gwilherm/midi-viscount-rte0616/firmware/firmware/USBMIDIInterface.h

#ifndef USB_MIDI_INTERFACE_H
#define USB_MIDI_INTERFACE_H

#include "IMIDIInterface.h"
#include "MIDIConfig.h"

#include <USB-MIDI.h>

class USBMIDIInterface : public IMIDIInterface {
public:
    USBMIDIInterface();
    virtual ~USBMIDIInterface() = default;

    void setup();
    void loop();

    virtual void sendSysEx(unsigned inLength,
                          const uint8_t* inArray);

    virtual void setHandleSystemExclusive(void (*fptr)(uint8_t * array, unsigned size));

    virtual void sendNote(IMIDIInterface::note_state_t state,
                          uint8_t inNoteNumber,
                          uint8_t inChannel);

    virtual void sendCC(uint8_t inControlNumber,
                        uint8_t inControlValue,
                        uint8_t inChannel);
protected:
    USBMIDI_NAMESPACE::usbMidiTransport _usbMidi;
    MIDI_NAMESPACE::MidiInterface<USBMIDI_NAMESPACE::usbMidiTransport> _usbMidiInterface;
};

#endif
