gwilherm/midi-viscount-rte0616/firmware/test/testsuite/MIDISysexServiceTest.cpp

#include <gtest/gtest.h>
#include <cstdint>

#include "SerialPrinter.h"
#include "MIDIConfig.h"
#include "CalibrationConfig.h"
#include "USBMIDIMock.h"
#include "MemoryServiceMock.h"
#include "MIDISysexService.h"

SerialPrinter Serial;

#define EXPECT_SYSEX(e) [&](unsigned size, const uint8_t* array) { \
    EXPECT_EQ(size, sizeof(e)); \
    for (int i = 0; i < sizeof(e); i++) \
        EXPECT_EQ(array[i], e[i]); \
}

class MIDISysexServiceTest : public ::testing::Test {
public:
    MIDISysexServiceTest() : _sysexService(_usbMidiMock, _midiConfig, _calibrationConfig, _memServiceMock)
    {};

    void SetUp(void) {
        _midiConfig.reset();
        _calibrationConfig.reset();
    }

protected:
    MidiConfig _midiConfig;
    CalibrationConfig _calibrationConfig;
    ::testing::StrictMock<USBMIDIMock> _usbMidiMock;
    MemoryServiceMock _memServiceMock;
    MIDISysexService _sysexService;
};

TEST_F(MIDISysexServiceTest, handle_ident_msg)
{
    // Ident request
    uint8_t req[] = { 0xF0, 0x7E, 0x7F, 0x06, 0x01, 0xF7 };
    //                                 chan,                     f1,   f2,   p1,   p2,   v1,   v2,   v3,   v4
    const uint8_t exp_resp[] = { 0x7E, 0x01, 0x06, 0x02, 0x31, 0x00, 0x31, 0x06, 0x16, 0x01, 0x02, 0x00, 0x03 };

    using namespace ::testing;
    EXPECT_CALL(_usbMidiMock, sendSysEx(_, _))
    .WillOnce(Invoke(EXPECT_SYSEX(exp_resp)));

    _sysexService.handleSysEx(req, sizeof(req));
}

TEST_F(MIDISysexServiceTest, handle_get_midi_config)
{
    uint8_t req[] = { 0xF0, 0x31, 0x06, 0x16, 0x01, 0x01, 0xF7 };
                                                             // Default values
    const uint8_t exp_resp1[] = { 0x31, 0x06, 0x16, 0x01, 0x00, 1, 3, 0 };

    using namespace ::testing;
    EXPECT_CALL(_usbMidiMock, sendSysEx(_, _))
    .WillOnce(Invoke(EXPECT_SYSEX(exp_resp1)));

    _sysexService.handleSysEx(req, sizeof(req));

    _midiConfig.setChannel(12);
    _midiConfig.setOctave(1);
    _midiConfig.setKeyboardMode(MidiConfig::POLYPHONIC);
    const uint8_t exp_resp2[] = { 0x31, 0x06, 0x16, 0x01, 0x00, 12, 1, 1 };

    EXPECT_CALL(_usbMidiMock, sendSysEx(_, _))
    .WillOnce(Invoke(EXPECT_SYSEX(exp_resp2)));

    _sysexService.handleSysEx(req, sizeof(req));
}

TEST_F(MIDISysexServiceTest, handle_store_midi_config)
{
    uint8_t req[] = { 0xF0, 0x31, 0x06, 0x16, 0x01, 0x03, 0xF7 };

    EXPECT_CALL(_memServiceMock, updateMidiConfig());

    _sysexService.handleSysEx(req, sizeof(req));
}

TEST_F(MIDISysexServiceTest, handle_set_midi_config)
{
    uint8_t req[] = { 0xF0, 0x31, 0x06, 0x16, 0x01, 0x02, 12, 6, 1, 0xF7 };
    const uint8_t exp_resp[] = { 0x31, 0x06, 0x16, 0x01, 0x00, 12, 6, 1 };

    using namespace ::testing;
    EXPECT_CALL(_usbMidiMock, sendSysEx(_, _))
    .WillOnce(Invoke(EXPECT_SYSEX(exp_resp)));

    _sysexService.handleSysEx(req, sizeof(req));

    EXPECT_EQ(_midiConfig.getChannel(), 12);
    EXPECT_EQ(_midiConfig.getOctave(), 6);
    EXPECT_EQ(_midiConfig.getKeyboardMode(), MidiConfig::POLYPHONIC);
}

TEST_F(MIDISysexServiceTest, handle_get_calibration_config)
{
    uint8_t req[] = { 0xF0, 0x31, 0x06, 0x16, 0x02, 0x01, 0xF7 };
                                                             // Default values
    const uint8_t exp_resp1[] = { 0x31, 0x06, 0x16, 0x02, 0x00, 0, 50, 6, 62, 4, 0, 2, 70, 0, 14 };
    // const uint8_t exp_resp1[] = { 0x31, 0x06, 0x16, 0x02, 0x00, 0, 50, 7, 37, 4, 113, 3, 58, 1, 2 };

    using namespace ::testing;
    EXPECT_CALL(_usbMidiMock, sendSysEx(_, _))
    .WillOnce(Invoke(EXPECT_SYSEX(exp_resp1)));

    _sysexService.handleSysEx(req, sizeof(req));

    _calibrationConfig.setMargin(12);
    _calibrationConfig.setVSeg(0, 1);
    _calibrationConfig.setVSeg(1, 2);
    _calibrationConfig.setVSeg(2, 3);
    _calibrationConfig.setVSeg(3, 4);

    const uint8_t exp_resp2[] = { 0x31, 0x06, 0x16, 0x02, 0x00, 0, 12, 0, 1, 0, 2, 0, 3, 0, 4 };

    EXPECT_CALL(_usbMidiMock, sendSysEx(_, _))
    .WillOnce(Invoke(EXPECT_SYSEX(exp_resp2)));

    _sysexService.handleSysEx(req, sizeof(req));
}

TEST_F(MIDISysexServiceTest, handle_store_calibration_config)
{
    uint8_t req[] = { 0xF0, 0x31, 0x06, 0x16, 0x02, 0x03, 0xF7 };

    EXPECT_CALL(_memServiceMock, updateCalibration());

    _sysexService.handleSysEx(req, sizeof(req));
}

TEST_F(MIDISysexServiceTest, handle_set_calibration_config)
{
    uint8_t req[] = { 0xF0, 0x31, 0x06, 0x16, 0x02, 0x02, 0, 12, 0, 1, 0, 2, 0, 3, 0, 4, 0xF7 };
    const uint8_t exp_resp[] = { 0x31, 0x06, 0x16, 0x02, 0x00, 0, 12, 0, 1, 0, 2, 0, 3, 0, 4 };

    using namespace ::testing;
    EXPECT_CALL(_usbMidiMock, sendSysEx(_, _))
    .WillOnce(Invoke(EXPECT_SYSEX(exp_resp)));

    _sysexService.handleSysEx(req, sizeof(req));

    EXPECT_EQ(_calibrationConfig.getMargin(), 12);
    EXPECT_EQ(_calibrationConfig.getVSeg(0), 1);
    EXPECT_EQ(_calibrationConfig.getVSeg(1), 2);
    EXPECT_EQ(_calibrationConfig.getVSeg(2), 3);
    EXPECT_EQ(_calibrationConfig.getVSeg(3), 4);
}

TEST_F(MIDISysexServiceTest, handle_measures_request)
{
    uint8_t req[] = { 0xF0, 0x31, 0x06, 0x16, 0x04, 0x02, 0xF7 };
    _sysexService.handleSysEx(req, sizeof(req));
    EXPECT_EQ(_sysexService.shouldSendMeasures(), true);
}

TEST_F(MIDISysexServiceTest, send_measures)
{
    int measures[] = { 1, 2, 3, 4, 5, 6, 7, 8 };
    const uint8_t exp_resp[] = { 0x31, 0x06, 0x16, 0x03, 0x00, 0, 1, 0, 2, 0, 3, 0, 4, 0, 5, 0, 6, 0, 7, 0, 8 };

    using namespace ::testing;
    EXPECT_CALL(_usbMidiMock, sendSysEx(_, _))
    .WillOnce(Invoke(EXPECT_SYSEX(exp_resp)));

    _sysexService.sendMeasures(measures, 8);
}

TEST_F(MIDISysexServiceTest, handle_factory_reset)
{
    uint8_t req[] = { 0xF0, 0x31, 0x06, 0x16, 0x7F, 0xF7 };

    EXPECT_CALL(_memServiceMock, factoryReset());

    _sysexService.handleSysEx(req, sizeof(req));
}
