gwilherm/midi-viscount-rte0616/firmware/test/testsuite/MIDICCServiceTest.cpp

#include <gtest/gtest.h>
#include "MIDIConfig.h"
#include "CalibrationConfig.h"
#include "ExtraPedalInterfaceMock.h"
#include "MIDICCService.h"
#include "USBMIDIMock.h"
#include "SerialPrinter.h"

SerialPrinter Serial;

using namespace ::testing;

class MIDICCServiceTest : public Test {
public:
    MIDICCServiceTest():
        _midiConfig(1, 3, MidiConfig::MONODIC_UP),
        _ccService(_usbMidiMock, _midiConfig, _extraPedalInterfaceMock)
    {};

protected:
    StrictMock<USBMIDIMock> _usbMidiMock;
    MidiConfig _midiConfig;
    ExtraPedalInterfaceMock _extraPedalInterfaceMock;
    MIDICCService _ccService;
};

TEST_F(MIDICCServiceTest, setup)
{
    _ccService.setup();
}

TEST_F(MIDICCServiceTest, loop)
{
    // Half expression
    EXPECT_CALL(_extraPedalInterfaceMock, getExpressionValue)
    .WillOnce(Return(512));
    EXPECT_CALL(_extraPedalInterfaceMock, getSwitchState)
    .WillRepeatedly(Return(true));

    
    EXPECT_CALL(_usbMidiMock, sendCC(11, 64, 1));
    EXPECT_CALL(_usbMidiMock, sendCC(64, 127, 1));

    _ccService.loop();
}
