gwilherm/midi-viscount-rte0616/firmware/test/testsuite/ArduinoTestFixture.h

#ifndef ARDUINO_TEST_FIXTURE_H
#define ARDUINO_TEST_FIXTURE_H

#include "ArduinoMock.h"

class ArduinoTestFixture: public ::testing::Test{
public:
    ArduinoTestFixture(){
        _arduinoMock.reset(new ::testing::NiceMock<ArduinoMock>());
    }
    ~ArduinoTestFixture(){
        _arduinoMock.reset();
    }
    virtual void SetUp(){}
    virtual void TearDown(){}

    // pointer for accessing mocked library
    static std::unique_ptr<::testing::NiceMock<ArduinoMock>> _arduinoMock;
};

#endif
